raghavbharath/usb-logic-analyzer/Digital_Logic_Analyzer.drawio.png

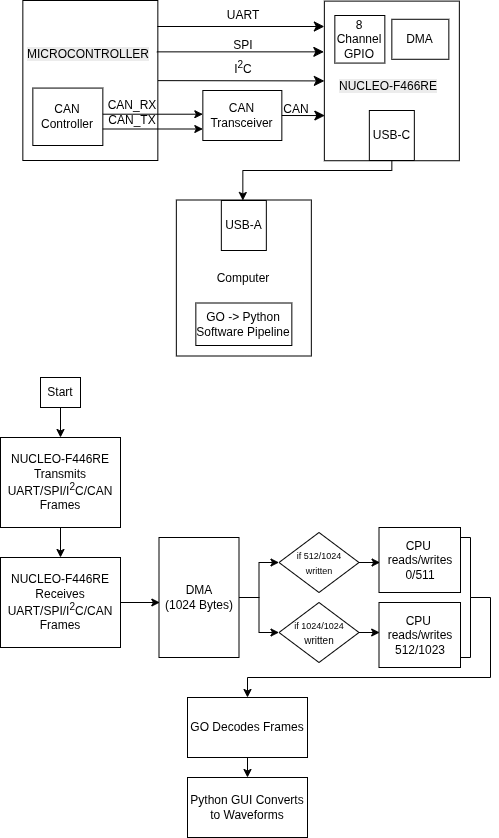
Digital_Logic_Analyzer.drawio.png
