raghavbharath/usb-logic-analyzer/firmware-receiver/docs/html/d0/d66/stm32f4xx__hal__dma_8c__incl.png

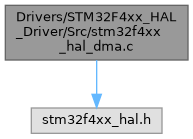
firmware-receiver/docs/html/d0/d66/stm32f4xx__hal__dma_8c__incl.png
