raghavbharath/usb-logic-analyzer/firmware-receiver/docs/html/d0/d89/group__STM32F4xx__HAL__Driver.png

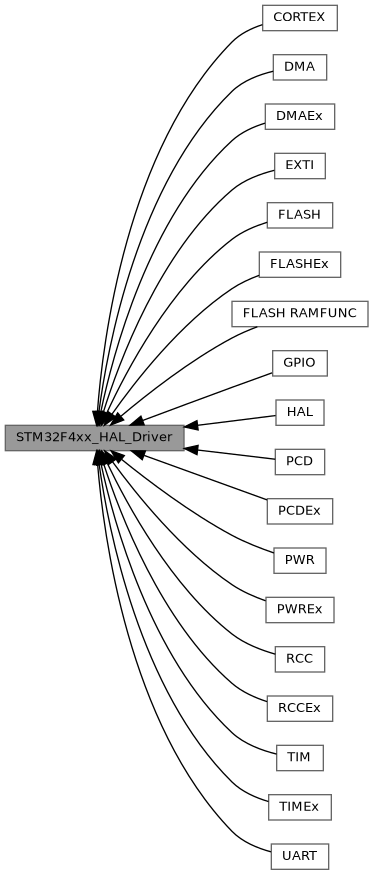
firmware-receiver/docs/html/d0/d89/group__STM32F4xx__HAL__Driver.png
