raghavbharath/usb-logic-analyzer/firmware-receiver/docs/html/d0/dd1/group__TIMEx__Exported__Functions.png

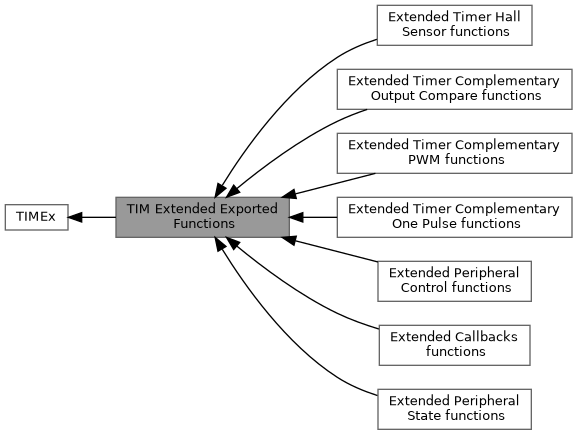
firmware-receiver/docs/html/d0/dd1/group__TIMEx__Exported__Functions.png
