raghavbharath/usb-logic-analyzer/firmware-receiver/docs/html/d1/d1c/stm32f4xx__hal__pcd__ex_8c__incl.png

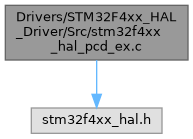
firmware-receiver/docs/html/d1/d1c/stm32f4xx__hal__pcd__ex_8c__incl.png
