raghavbharath/usb-logic-analyzer/firmware-receiver/docs/html/d1/d2d/group__FLASH__Exported__Functions.png

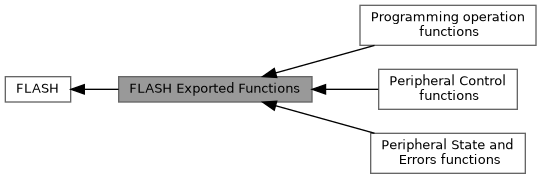
firmware-receiver/docs/html/d1/d2d/group__FLASH__Exported__Functions.png
