raghavbharath/usb-logic-analyzer/firmware-receiver/docs/html/d2/d83/stm32f4xx__hal__msp_8c__incl.png

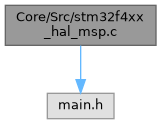
firmware-receiver/docs/html/d2/d83/stm32f4xx__hal__msp_8c__incl.png
