raghavbharath/usb-logic-analyzer/firmware-receiver/docs/html/d2/dbf/group__HAL.png

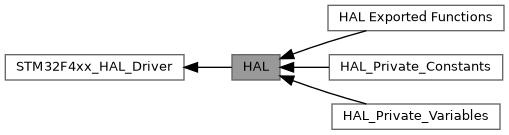
firmware-receiver/docs/html/d2/dbf/group__HAL.png
