raghavbharath/usb-logic-analyzer/firmware-receiver/docs/html/d5/d4c/group__FLASHEx.png

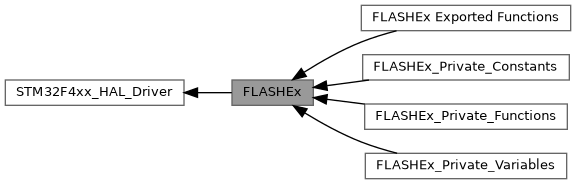
firmware-receiver/docs/html/d5/d4c/group__FLASHEx.png
