raghavbharath/usb-logic-analyzer/firmware-receiver/docs/html/d5/d49/group__USBD__CDC__IF.png

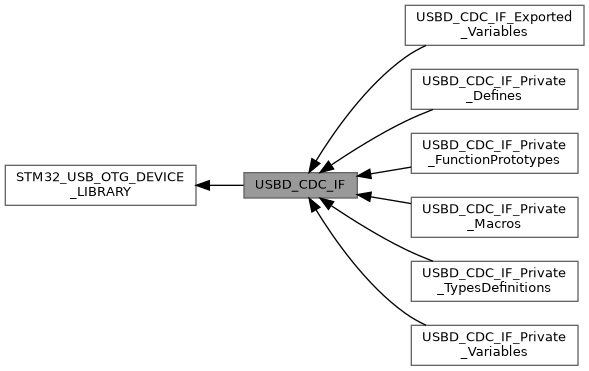
firmware-receiver/docs/html/d5/d49/group__USBD__CDC__IF.png
