raghavbharath/usb-logic-analyzer/firmware-receiver/docs/html/d6/d0b/usbd__desc_8c__incl.png

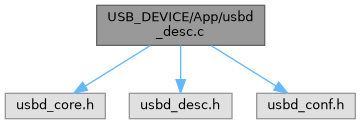
firmware-receiver/docs/html/d6/d0b/usbd__desc_8c__incl.png
