raghavbharath/usb-logic-analyzer/firmware-receiver/docs/html/d6/d0e/group__TIM__Exported__Functions.png

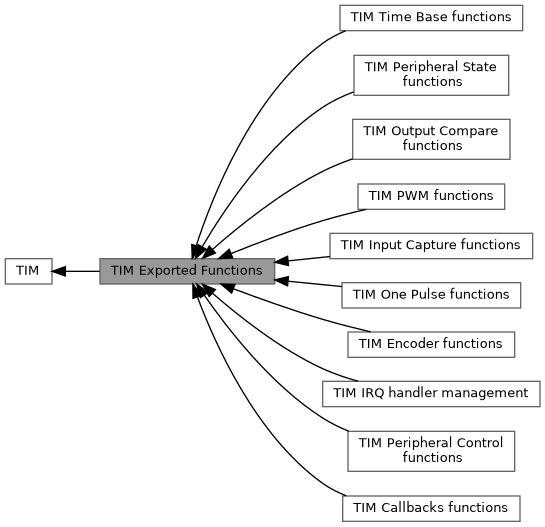
firmware-receiver/docs/html/d6/d0e/group__TIM__Exported__Functions.png
