raghavbharath/usb-logic-analyzer/firmware-receiver/docs/html/d8/d1b/stm32f4xx__hal_8c__incl.png

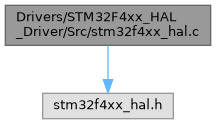
firmware-receiver/docs/html/d8/d1b/stm32f4xx__hal_8c__incl.png
