raghavbharath/usb-logic-analyzer/firmware-receiver/docs/html/d8/db2/usbd__cdc__if_8c__incl.png

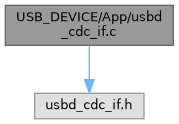
firmware-receiver/docs/html/d8/db2/usbd__cdc__if_8c__incl.png
