raghavbharath/usb-logic-analyzer/firmware-receiver/docs/html/db/dfe/group__stm32f4xx__system.png

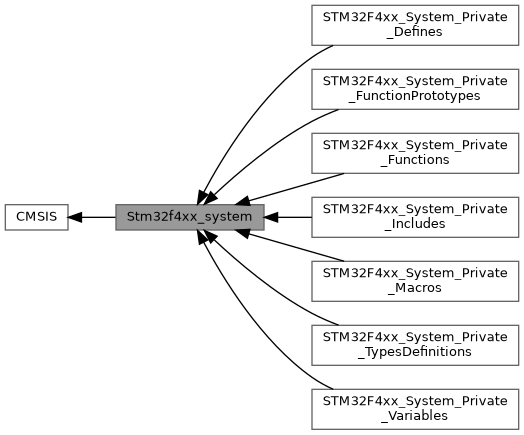
firmware-receiver/docs/html/db/dfe/group__stm32f4xx__system.png
