raghavbharath/usb-logic-analyzer/firmware-receiver/docs/html/dc/dd9/group__USBD__DESC.png

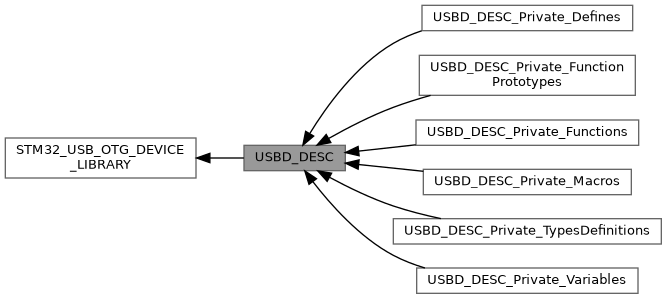
firmware-receiver/docs/html/dc/dd9/group__USBD__DESC.png
