raghavbharath/usb-logic-analyzer/firmware-receiver/docs/html/de/d3f/group__DMA__Exported__Functions.png

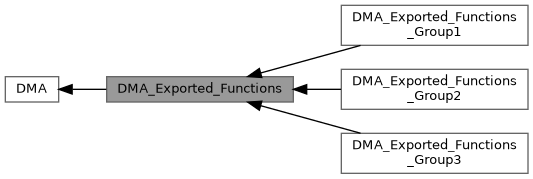
firmware-receiver/docs/html/de/d3f/group__DMA__Exported__Functions.png
