raghavbharath/usb-logic-analyzer/firmware-receiver/docs/html/dir_0f7073d6b1d1d49104212e142cbd4b45_dep.png

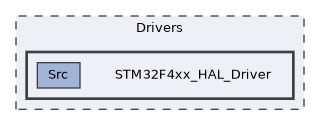
firmware-receiver/docs/html/dir_0f7073d6b1d1d49104212e142cbd4b45_dep.png
