raghavbharath/usb-logic-analyzer/firmware-receiver/docs/html/graph_legend.png

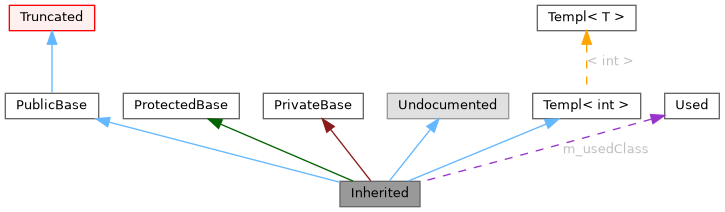
firmware-receiver/docs/html/graph_legend.png
