raghavbharath/usb-logic-analyzer/SignalDecoder/assets/uart_diagram.png

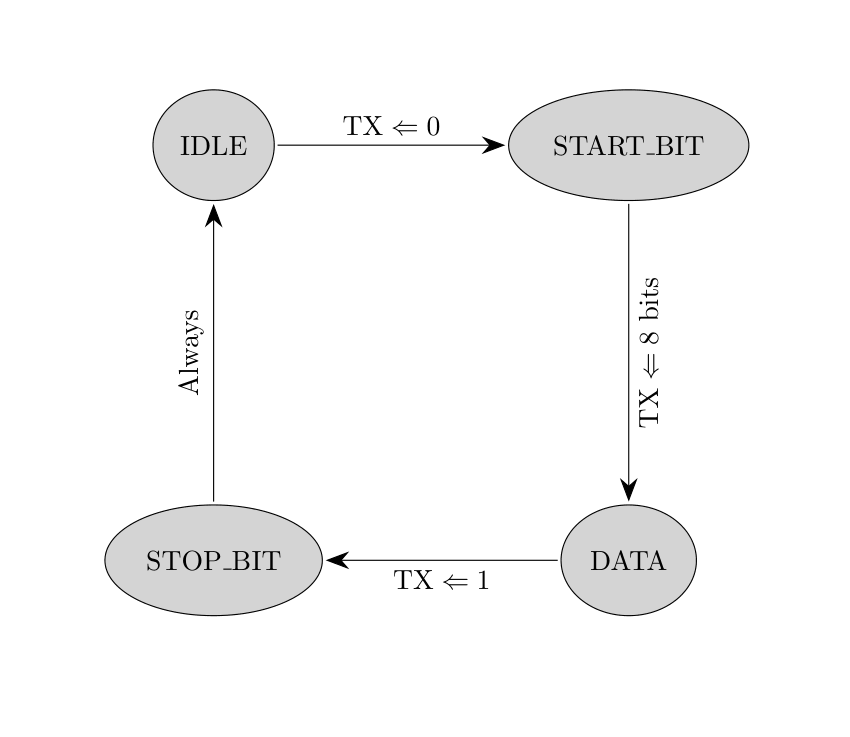
SignalDecoder/assets/uart_diagram.png
